TinyCircuits/TinyCircuits-TinyShield-Memory-EEPROM-ASD2202/cad/TinyShield_EEPROM_ASD2202_REV3-DETAILED_DRAWING-PNG.png

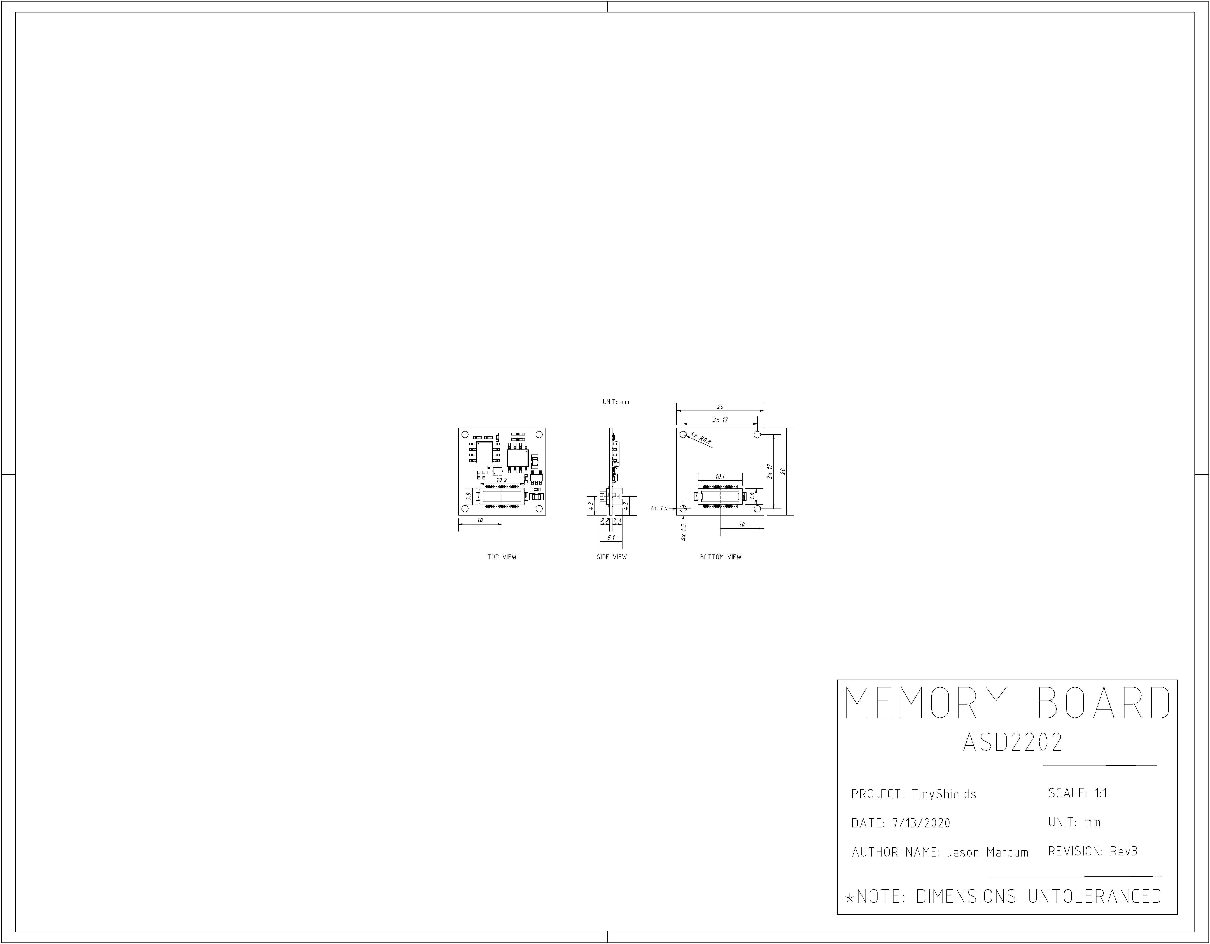
cad/TinyShield_EEPROM_ASD2202_REV3-DETAILED_DRAWING-PNG.png
