TinyCircuits/TinyCircuits-TinyShield-Memory-EEPROM-ASD2202/images/EEPROM/ASD2202-R-E-Tutorial-Image-01.jpg

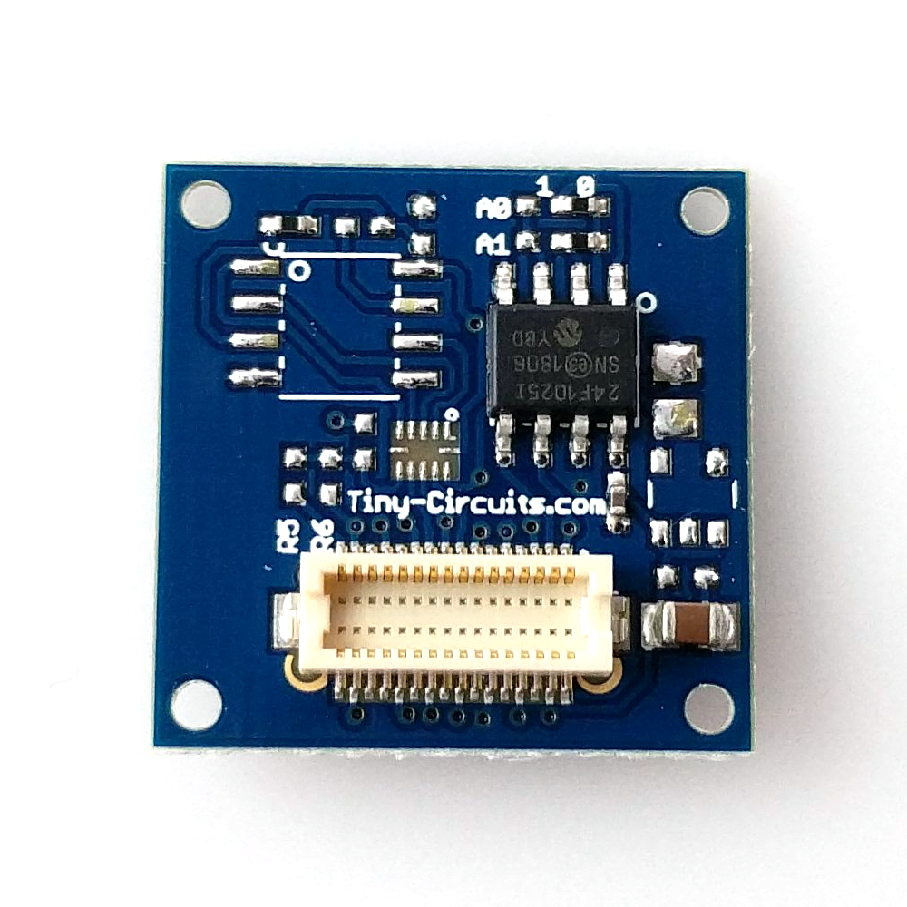
images/EEPROM/ASD2202-R-E-Tutorial-Image-01.jpg
