TinyCircuits/TinyCircuits-TinyShield-Memory-EEPROM-ASD2202/images/EEPROM/ASD2202-R-E-Tutorial-Image-03.jpg

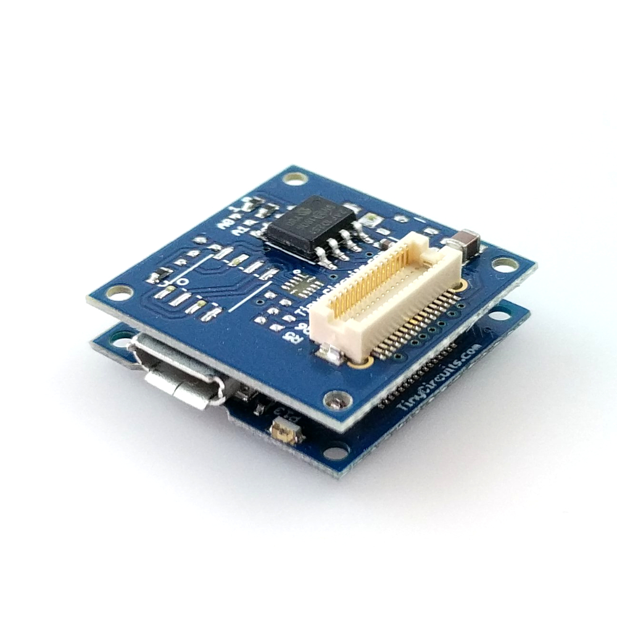
images/EEPROM/ASD2202-R-E-Tutorial-Image-03.jpg
