TinyCircuits/TinyCircuits-TinyShield-Memory-EEPROM-ASD2202/images/EEPROM/ASD2202-R-E-Tutorial-Image-04.png

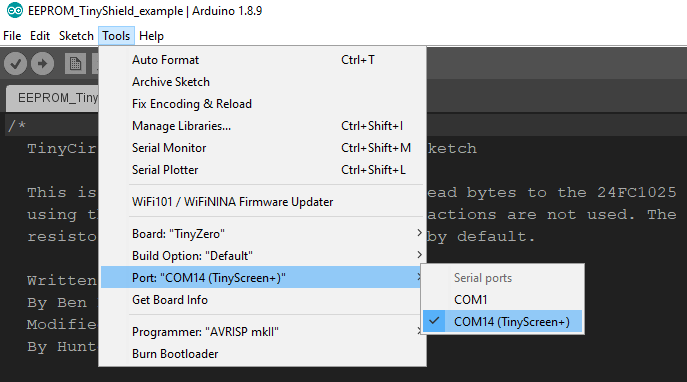
images/EEPROM/ASD2202-R-E-Tutorial-Image-04.png
