TinyCircuits/TinyCircuits-TinyShield-Memory-EEPROM-ASD2202/images/Flash Memory/ASD2202-R-F-Tutorial-Image-01.png

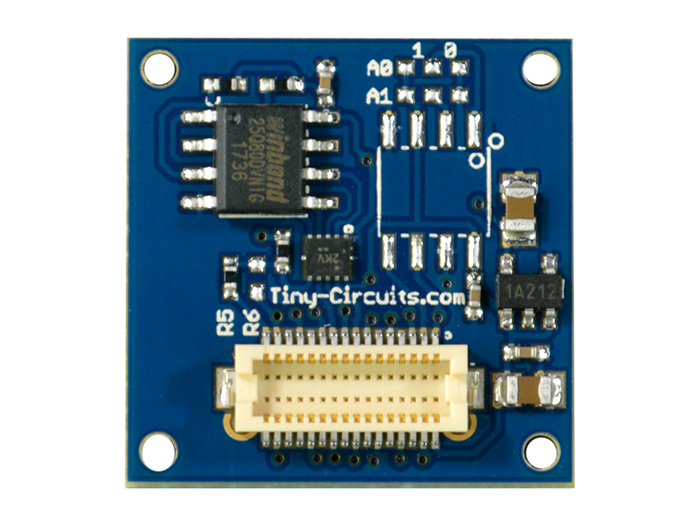
images/Flash Memory/ASD2202-R-F-Tutorial-Image-01.png
