TinyCircuits/TinyCircuits-TinyShield-Memory-EEPROM-ASD2202/images/SRAM/ASD2202-R-S-Tutorial-Image-01.png

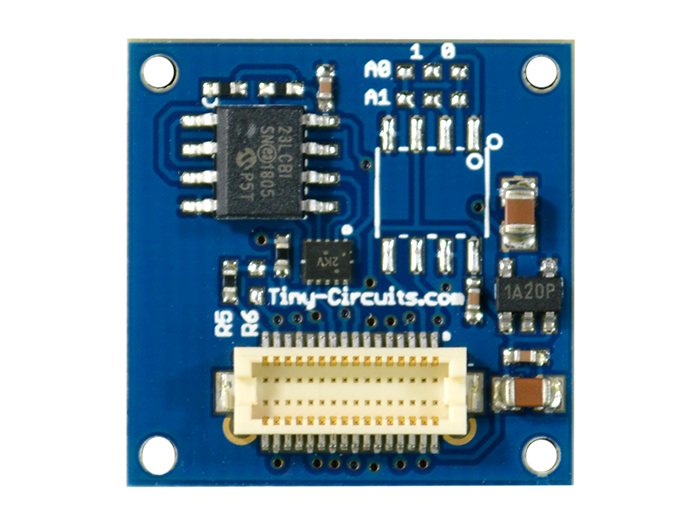
images/SRAM/ASD2202-R-S-Tutorial-Image-01.png
