TinyCircuits/TinyCircuits-TinyShield-Memory-EEPROM-ASD2202/images/SRAM/ASD2202-R-S-Tutorial-Image-06.png

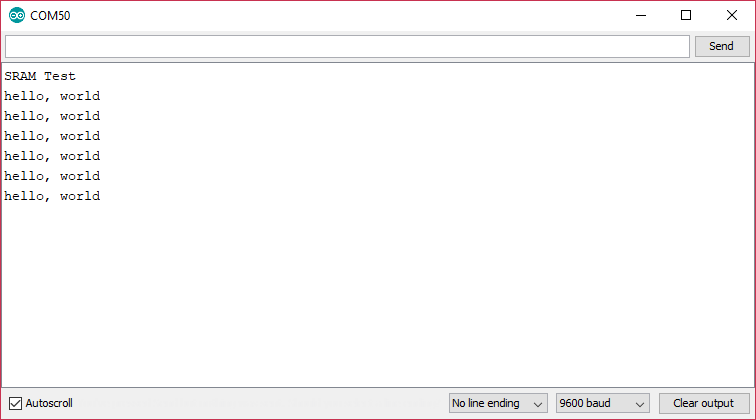
images/SRAM/ASD2202-R-S-Tutorial-Image-06.png
