TinyCircuits/TinyCircuits-TinyShield-Memory-EEPROM-ASD2202/examples/EEPROM_TinyShield_example/EEPROM_TinyShield_example.ino

/*
  TinyCircuits EEPROM TinyShield Example Sketch
  
  This is an example of how to write and read bytes to the 24FC1025 I2C EEPROM
  using the Wire library. Page write transactions are not used. The address
  resistors on the board are both low (0) by default.

  Written 03 May 2016
  By Ben Rose
  Modified 07 January 2019
  By Hunter Hykes

  https://TinyCircuits.com
*/

#include <Wire.h>

#define EEPROM_A0 0
#define EEPROM_A1 0
#define EEPROM_ADDR 0x50|(EEPROM_A1<<1)|(EEPROM_A0<<0)

// Decide what Serial port to use!
#ifdef ARDUINO_ARCH_SAMD
  #define SerialMonitor SerialUSB // Our TinyScreen+ is an SAMD board.
#else
  #define SerialMonitor Serial
#endif

void setup() {
  Wire.begin();
  SerialMonitor.begin(115200);
  while(!SerialMonitor); // Halts program until Serial Monitor is opened
  SerialMonitor.println("Writing..");
  char writeData[]="TinyCircuits!";
  EEPROMwrite(0,(uint8_t*)writeData,sizeof(writeData));
  char readData[]="If you see this, there's an error!";
  SerialMonitor.println("Reading..");
  EEPROMread(0,(uint8_t*)readData,sizeof(writeData));
  SerialMonitor.println(readData);
}

void loop() {
  // put your main code here, to run repeatedly:
//  SerialUSB.print("test");

}

void EEPROMread(unsigned long addr, uint8_t* buff, unsigned long count){
  for(unsigned long i=0;i<count;i++){
    buff[i]=EEPROMread(addr+i);
  }
}

void EEPROMwrite(unsigned long addr, uint8_t* buff, unsigned long count){
  for(unsigned long i=0;i<count;i++){
    EEPROMwrite(addr+i,buff[i]);
  }
}

byte EEPROMread(unsigned long addr){
  uint8_t val=255;
  uint8_t I2Caddr=EEPROM_ADDR;
  if(addr>0x0000FFFF){
    I2Caddr|=0x04;
  }
  Wire.beginTransmission(I2Caddr);
  Wire.write(addr>>8);
  Wire.write(addr);
  Wire.endTransmission();
  Wire.requestFrom(I2Caddr,(uint8_t)1);
  while(Wire.available()){
    val=Wire.read();
  }
  return val;
}

byte EEPROMwrite(unsigned long addr, byte val){
  uint8_t I2Caddr=EEPROM_ADDR;
  if(addr>0x0000FFFF){
    I2Caddr|=0x04;
  }
  Wire.beginTransmission(I2Caddr);
  Wire.write(addr>>8);
  Wire.write(addr);
  Wire.write(val);
  Wire.endTransmission();
  Wire.beginTransmission(I2Caddr);
  unsigned long timeout=millis();
  while(Wire.endTransmission() && millis()-timeout<10){
    Wire.beginTransmission(I2Caddr);
  }
}
